anwa/esphome-r4875g1-3phase-charger/packages/display/pages/cooling.yaml

# ==============================================================================
# SHARED V6 LVGL PAGE: COOLING
# ==============================================================================
#
# Cooling overview for the three internal Huawei rectifier fans and the shared
# rear-compartment temperature, humidity and sea-level pressure measurements.
#
# Fan-mode controls express user intent through the shared UI command boundary.
# Controller-only external chassis-fan control is not exposed on this page.
#
# Runtime updates are handled by display/cooling.yaml.
# ==============================================================================

id: page_cooling
styles: style_page

widgets:

  # ---------------------------------------------------------------------------
  # COMPARTMENT ENVIRONMENT
  # ---------------------------------------------------------------------------

  - obj:
      x: 10
      y: 70
      width: 780
      height: 55
      styles: style_card

      widgets:
        - label:
            x: 10
            y: 10
            styles: style_title_label
            text: "COMPARTMENT"

        - label:
            id: ui_cooling_compartment_temperature
            x: 170
            y: 13
            width: 170
            text_align: CENTER
            text: "--.- °C"
            text_font: montserrat_24
            text_color: 0xFFFFFF

        - label:
            id: ui_cooling_compartment_humidity
            x: 375
            y: 13
            width: 170
            text_align: CENTER
            text: "--.- %"
            text_font: montserrat_24
            text_color: 0xFFFFFF

        - label:
            id: ui_cooling_compartment_pressure
            x: 580
            y: 13
            width: 180
            text_align: CENTER
            text: "----.- hPa"
            text_font: montserrat_24
            text_color: 0xFFFFFF

  # ---------------------------------------------------------------------------
  # RECTIFIER 1 FAN
  # ---------------------------------------------------------------------------

  - obj:
      x: 10
      y: 135
      width: 253
      height: 265
      styles: style_card

      widgets:
        - label:
            x: 10
            y: 10
            styles: style_title_label
            text: "RECTIFIER 1 FAN"

        - label:
            id: ui_cooling_r1_state
            x: 10
            y: 38
            width: 230
            text: "OFFLINE"
            text_font: montserrat_14
            text_color: 0x8B96A0

        - label:
            id: ui_cooling_r1_rpm
            x: 10
            y: 68
            width: 230
            text_align: CENTER
            text: "---- RPM"
            text_font: montserrat_24
            text_color: 0xFFFFFF

        - label:
            x: 10
            y: 108
            styles: style_desc_label
            text: "Minimum"

        - label:
            id: ui_cooling_r1_min_duty
            x: 130
            y: 106
            width: 110
            styles: style_value_label
            text: "--.- %"

        - label:
            x: 10
            y: 136
            styles: style_desc_label
            text: "Target"

        - label:
            id: ui_cooling_r1_target_duty
            x: 130
            y: 134
            width: 110
            styles: style_value_label
            text: "--.- %"

        - label:
            id: ui_cooling_r1_temperature
            x: 10
            y: 164
            width: 110
            text: "--.- °C"
            text_font: montserrat_16
            text_color: 0xDDE3E8

        - label:
            id: ui_cooling_r1_thermal
            x: 130
            y: 164
            width: 110
            text_align: RIGHT
            text: "--"
            text_font: montserrat_16
            text_color: 0x8B96A0

        - button:
            id: ui_cooling_r1_auto_button
            x: 10
            y: 205
            width: 110
            styles: style_dialog_button
            state:
              disabled: true

            widgets:
              - label:
                  align: CENTER
                  text: "AUTO"
                  text_font: montserrat_16

            on_short_click:
              - script.execute:
                  id: ui_command_rectifier_fan_auto
                  unit: 1

        - button:
            id: ui_cooling_r1_full_button
            x: 130
            y: 205
            width: 110
            styles: style_dialog_button
            state:
              disabled: true

            widgets:
              - label:
                  align: CENTER
                  text: "FULL"
                  text_font: montserrat_16

            on_short_click:
              - script.execute:
                  id: ui_command_rectifier_fan_full
                  unit: 1

  # ---------------------------------------------------------------------------
  # RECTIFIER 2 FAN
  # ---------------------------------------------------------------------------

  - obj:
      x: 273
      y: 135
      width: 253
      height: 265
      styles: style_card

      widgets:
        - label:
            x: 10
            y: 10
            styles: style_title_label
            text: "RECTIFIER 2 FAN"

        - label:
            id: ui_cooling_r2_state
            x: 10
            y: 38
            width: 230
            text: "OFFLINE"
            text_font: montserrat_14
            text_color: 0x8B96A0

        - label:
            id: ui_cooling_r2_rpm
            x: 10
            y: 68
            width: 230
            text_align: CENTER
            text: "---- RPM"
            text_font: montserrat_24
            text_color: 0xFFFFFF

        - label:
            x: 10
            y: 108
            styles: style_desc_label
            text: "Minimum"

        - label:
            id: ui_cooling_r2_min_duty
            x: 130
            y: 106
            width: 110
            styles: style_value_label
            text: "--.- %"

        - label:
            x: 10
            y: 136
            styles: style_desc_label
            text: "Target"

        - label:
            id: ui_cooling_r2_target_duty
            x: 130
            y: 134
            width: 110
            styles: style_value_label
            text: "--.- %"

        - label:
            id: ui_cooling_r2_temperature
            x: 10
            y: 164
            width: 110
            text: "--.- °C"
            text_font: montserrat_16
            text_color: 0xDDE3E8

        - label:
            id: ui_cooling_r2_thermal
            x: 130
            y: 164
            width: 110
            text_align: RIGHT
            text: "--"
            text_font: montserrat_16
            text_color: 0x8B96A0

        - button:
            id: ui_cooling_r2_auto_button
            x: 10
            y: 205
            width: 110
            styles: style_dialog_button
            state:
              disabled: true

            widgets:
              - label:
                  align: CENTER
                  text: "AUTO"
                  text_font: montserrat_16

            on_short_click:
              - script.execute:
                  id: ui_command_rectifier_fan_auto
                  unit: 2

        - button:
            id: ui_cooling_r2_full_button
            x: 130
            y: 205
            width: 110
            styles: style_dialog_button
            state:
              disabled: true

            widgets:
              - label:
                  align: CENTER
                  text: "FULL"
                  text_font: montserrat_16

            on_short_click:
              - script.execute:
                  id: ui_command_rectifier_fan_full
                  unit: 2

  # ---------------------------------------------------------------------------
  # RECTIFIER 3 FAN
  # ---------------------------------------------------------------------------

  - obj:
      x: 536
      y: 135
      width: 253
      height: 265
      styles: style_card

      widgets:
        - label:
            x: 10
            y: 10
            styles: style_title_label
            text: "RECTIFIER 3 FAN"

        - label:
            id: ui_cooling_r3_state
            x: 10
            y: 38
            width: 230
            text: "OFFLINE"
            text_font: montserrat_14
            text_color: 0x8B96A0

        - label:
            id: ui_cooling_r3_rpm
            x: 10
            y: 68
            width: 230
            text_align: CENTER
            text: "---- RPM"
            text_font: montserrat_24
            text_color: 0xFFFFFF

        - label:
            x: 10
            y: 108
            styles: style_desc_label
            text: "Minimum"

        - label:
            id: ui_cooling_r3_min_duty
            x: 130
            y: 106
            width: 110
            styles: style_value_label
            text: "--.- %"

        - label:
            x: 10
            y: 136
            styles: style_desc_label
            text: "Target"

        - label:
            id: ui_cooling_r3_target_duty
            x: 130
            y: 134
            width: 110
            styles: style_value_label
            text: "--.- %"

        - label:
            id: ui_cooling_r3_temperature
            x: 10
            y: 164
            width: 110
            text: "--.- °C"
            text_font: montserrat_16
            text_color: 0xDDE3E8

        - label:
            id: ui_cooling_r3_thermal
            x: 130
            y: 164
            width: 110
            text_align: RIGHT
            text: "--"
            text_font: montserrat_16
            text_color: 0x8B96A0

        - button:
            id: ui_cooling_r3_auto_button
            x: 10
            y: 205
            width: 110
            styles: style_dialog_button
            state:
              disabled: true

            widgets:
              - label:
                  align: CENTER
                  text: "AUTO"
                  text_font: montserrat_16

            on_short_click:
              - script.execute:
                  id: ui_command_rectifier_fan_auto
                  unit: 3

        - button:
            id: ui_cooling_r3_full_button
            x: 130
            y: 205
            width: 110
            styles: style_dialog_button
            state:
              disabled: true

            widgets:
              - label:
                  align: CENTER
                  text: "FULL"
                  text_font: montserrat_16

            on_short_click:
              - script.execute:
                  id: ui_command_rectifier_fan_full
                  unit: 3
