anwa/esphome-r4875g1-3phase-charger/r4875g1-3phase-charger.yaml

# ==============================================================================
# R4875G1 THREE-PHASE CHARGER - V6 CONTROLLER HARDWARE
# ==============================================================================
#
# Target controller:
#   Waveshare ESP32-S3-Touch-LCD-7
#   ESP32-S3 N16R8
#
# Memory:
#   Flash -> 16 MB
#   PSRAM -> 8 MB Octal
#
# Integrated board hardware:
#   - 7-inch 800x480 RGB IPS display
#   - GT911 capacitive touch controller
#   - CH422G I/O expander
#   - onboard CAN transceiver
#   - onboard RS485 interface
#   - TF card interface
#   - native USB and USB-to-UART
#
# External hardware:
#   - dedicated external I2C bus on GPIO44 / GPIO43
#   - MCP23017 I/O expander @ 0x20
#   - BME280 compartment environment sensor @ 0x76
#   - EMC2101 external cooling-fan controller @ 0x4C
#   - backup rotary encoder on GPIO11 / GPIO12 / GPIO13
#   - external three/four-pin cooling-fan interface
#   - 1S lithium controller backup battery on J3
#   - battery-voltage measurement through TP1 / J8 AD / GPIO6
#
# The V6 Charger Controller retains the proven three-rectifier CAN control architecture
# while using the Waveshare display controller as the local standalone UI.
# ==============================================================================

# ==============================================================================
# THREE-PHASE R4875G1 CHARGER CONTROLLER - ARCHITECTURE OVERVIEW
# ==============================================================================
#
# This ESPHome firmware controls three Huawei R4875G1 rectifier units used as
# a three-phase battery charger. Each rectifier is supplied from one AC phase;
# their DC outputs are connected in parallel to the same battery bus.
#
# Data path:
#
#   R4875G1 Unit 1 / 2 / 3
#          |
#          | extended 29-bit CAN frames @ 125 kbit/s
#          v
#   ESP32-S3 CAN decoder
#          |
#          +--> individual unit telemetry sensors
#          |      AC/DC power, voltage, current, frequency, temperatures, state
#          |
#          +--> per-unit CAN watchdogs (can_com_ok_1..3)
#          |
#          +--> CAN-aware charger-wide aggregate telemetry
#          |
#          +--> TFT display / Home Assistant / MQTT
#
# Local control path:
#
#   GT911 touchscreen / LVGL interface
#          |
#          +--> charger-wide voltage and power setpoints
#          +--> charger and per-unit START/STOP controls
#          +--> fallback voltage/current adjustment
#
# The backup rotary encoder provides a local staged editor for the charger-wide
# DC voltage and nominal DC sum-power setpoints. Saved values use the same
# authoritative command path as the touchscreen. A deliberate long button
# press provides local charger START/STOP while the setpoint editor is idle.
# Power requests use the existing authoritative Charger Controller command
# paths rather than implementing separate CAN or safety logic.
#
# Offline operation:
#
# Wi-Fi, MQTT and Home Assistant are optional for core charger operation.
# Network reboot timeouts are disabled so a dead or isolated site network cannot
# prevent the ESP32 from controlling the charger during a blackstart.
#
# CAN value scaling:
#
# Most voltage/telemetry values use a fixed-point scale of 1024:
#     engineering_value = raw_CAN_value / 1024
#     raw_CAN_value     = engineering_value * 1024
#
# DC current commands use current_scaling_factor.
#
# Until all currently reachable rectifiers have fresh capability data, the
# controller uses the conservative 75 A protocol scale:
#
#     current_scaling_factor = 1024 / 75
#
# Once capability discovery is complete, command scaling is derived from the
# reachable rectifier capabilities.
#
# effective_dc_current_limit is maintained independently and enforces the
# lowest supported current capability across the currently reachable units.
# This keeps mixed-capability installations within the limit of the weakest
# available rectifier.
#
# Communication health:
#
# Valid per-unit CAN activity refreshes last_can_rx_1..3. During normal
# operation cyclic telemetry provides the heartbeat; valid property frames also
# refresh it while discovery temporarily suspends cyclic polling.
#
# If no valid CAN activity is received within can_watchdog_timeout_ms,
# can_com_ok_x becomes false. Display and aggregate logic then ignore stale
# values from that unit.
# ==============================================================================

substitutions:
  # ---------------------------------------------------------------------------
  # PROJECT IDENTITY
  # ---------------------------------------------------------------------------

  mqtt_command_prefix: "HG/DG/Technik/Charger"
  fallback_ap_ssid: "Charger Fallback Hotspot"
  diagnostics_device_label: "Controller"

  # ---------------------------------------------------------------------------
  # INSTALLATION ENVIRONMENT
  # ---------------------------------------------------------------------------
  # Fixed site altitude used for standard-atmosphere sea-level pressure
  # correction of the compartment BME280 station-pressure measurement.
  installation_altitude_m: "316.0"

  # ---------------------------------------------------------------------------
  # V6 CHARGER CONTROLLER GPIO MAP
  # ---------------------------------------------------------------------------

  pin_touch_irq: "GPIO4"
  pin_i2c_sda: "GPIO8"
  pin_i2c_scl: "GPIO9"
  pin_external_i2c_sda: "GPIO44"
  pin_external_i2c_scl: "GPIO43"
  pin_can_tx: "GPIO20"
  pin_can_rx: "GPIO19"
  pin_battery_adc: "GPIO6"

  # GPIO11/GPIO12/GPIO13 are the unused TF-card SPI pins.
  pin_backup_encoder_a: "GPIO11"
  pin_backup_encoder_b: "GPIO12"
  pin_backup_encoder_button: "GPIO13"

  # MCP23017 pin allocation.
  mcp_fan_enable_pin: "0"
  mcp_fan1_tach_pin: "1"
  mcp_fan2_tach_pin: "2"

  # ---------------------------------------------------------------------------
  # BACKUP ROTARY ENCODER
  # ---------------------------------------------------------------------------

  # One output step per complete quadrature cycle.
  backup_encoder_resolution: "1"

  # Pending setpoint edits are discarded after 15 seconds without activity.
  backup_encoder_edit_timeout_ms: "15000"

  # Transient encoder status overlays remain visible for 1.5 seconds.
  backup_encoder_ui_status_timeout_ms: "1500"

  # ---------------------------------------------------------------------------
  # DISPLAY DEFAULTS
  # ---------------------------------------------------------------------------

  ui_local_battery_label: "CTRL"
  display_idle_timeout: "60s"
  display_motion_entity: "binary_sensor.hg_og_buro_hg_og_buro_precense_occupancy"

  # ---------------------------------------------------------------------------
  # EXTERNAL COOLING-FAN DEFAULTS
  # ---------------------------------------------------------------------------

  # EMC2101 PWM configuration:
  #   360 kHz / (2 × 7 × 1) ≈ 25.7 kHz
  cooling_fan_pwm_resolution: "7"
  cooling_fan_pwm_divider: "1"

  cooling_fan_default_pwm_percent: "100.0"

  # Used for the two MCP23017-based tachometer inputs.
  cooling_fan_tach_pulses_per_revolution: "2.0"

  # ---------------------------------------------------------------------------
  # DC OPERATING LIMITS
  # ---------------------------------------------------------------------------

  # Absolute supported per-rectifier project ceiling.
  project_max_dc_current_a: "75.0"

  # Conservative ceiling until every currently reachable rectifier has a
  # freshly confirmed maximum-current capability.
  failsafe_dc_current_a: "50.0"

  minimum_dc_current_a: "1.0"

  dc_voltage_default_v: "53.0"

  # ---------------------------------------------------------------------------
  # THERMAL DERATING
  # ---------------------------------------------------------------------------

  thermal_warn1_c: "70.0"
  thermal_warn1_reset_c: "65.0"
  thermal_warn1_limit_a: "50.0"

  thermal_warn2_c: "80.0"
  thermal_warn2_reset_c: "75.0"
  thermal_warn2_limit_a: "30.0"

  overtemp_trip_c: "90.0"
  overtemp_reset_c: "80.0"

  # ---------------------------------------------------------------------------
  # THERMAL STATE CODES
  # ---------------------------------------------------------------------------

  thermal_state_normal: "0"
  thermal_state_warn1: "1"
  thermal_state_warn2: "2"
  thermal_state_lockout: "3"

  # Ignore near-idle input power where calculated efficiency becomes unstable.
  efficiency_min_ac_power_w: "100.0"

  # ---------------------------------------------------------------------------
  # PROTOCOL SCALING
  # ---------------------------------------------------------------------------

  protocol_value_scale: "1024"
  fan_duty_counts_per_percent: "256.0"

  # ---------------------------------------------------------------------------
  # RECTIFIER CONTROL-STATE CODES
  # ---------------------------------------------------------------------------
  # Internal lifecycle state used independently for each rectifier.
  #
  # OFFLINE:
  #   No usable communication / unit not operationally released.
  #
  # DISCOVERING:
  #   CAN communication has been detected, but discovery and validation have
  #   not yet completed.
  #
  # ONLINE:
  #   Discovery completed successfully and the unit is ready for normal
  #   operational handling.
  # ---------------------------------------------------------------------------

  rectifier_state_offline: "0"
  rectifier_state_discovering: "1"
  rectifier_state_online: "2"

  # ---------------------------------------------------------------------------
  # CAN COMMUNICATION
  # ---------------------------------------------------------------------------

  # RX queue depth must accommodate the largest observed multi-frame property
  # response without dropping frames.
  can_rx_queue_len: "64"

  # Normal runtime CAN watchdog.
  can_watchdog_timeout_ms: "3000"

  # Grace period after property discovery so normal cyclic polling has enough
  # time to resume before lifecycle connectivity is evaluated again.
  property_poll_resume_grace_ms: "2000"

  live_telemetry_timeout: "5s"

  telemetry_poll_interval: "577ms"
  fan_query_delay: "27ms"
  unit_2_poll_gap: "156ms"
  unit_3_poll_gap: "166ms"

  # Offline rectifiers are probed round-robin. One unit is considered every
  # five seconds, resulting in a maximum probe interval of approximately
  # 15 seconds per offline rectifier.
  offline_probe_slot_interval: "5s"

  can_recovery_check_interval: "2s"
  setpoint_refresh_interval: "30s"

  # ---------------------------------------------------------------------------
  # SLOW-CHANGING TELEMETRY
  # ---------------------------------------------------------------------------
  #
  # Stable diagnostic values are forwarded immediately when they change and
  # repeated periodically so time-series consumers retain a recent sample even
  # when the underlying charger state remains unchanged.
  # ---------------------------------------------------------------------------

  telemetry_heartbeat_interval: "60min"

  # ---------------------------------------------------------------------------
  # DISCOVERY RETRY POLICY
  # ---------------------------------------------------------------------------

  property_discovery_attempts: "3"
  capability_discovery_attempts: "10"
  discovery_retry_delay: "1s"
  discovery_startup_delay: "5s"
  property_bus_quiet_delay: "500ms"

# ==============================================================================
# FIRMWARE PACKAGE ASSEMBLY
# ==============================================================================
#
# Composes shared board hardware, Charger Controller hardware and the charger
# runtime packages, then instantiates one rectifier package per charger unit.
# ==============================================================================

packages:
  version: !include packages/version.yaml
  shared_ui_contract: !include packages/shared/ui-contract.yaml

  shared_core: !include packages/shared/core.yaml
  shared_local_diagnostics: !include packages/shared/local-diagnostics.yaml
  shared_hardware: !include packages/shared/hardware.yaml
  shared_ui_model: !include packages/shared/ui-model.yaml
  shared_ui_rectifier_1: !include
    file: packages/shared/ui-rectifier-unit.yaml
    vars:
      ui_unit: "1"

  shared_ui_rectifier_2: !include
    file: packages/shared/ui-rectifier-unit.yaml
    vars:
      ui_unit: "2"

  shared_ui_rectifier_3: !include
    file: packages/shared/ui-rectifier-unit.yaml
    vars:
      ui_unit: "3"

  shared_battery_monitoring: !include packages/shared/battery-monitoring.yaml

  controller_hardware: !include packages/controller/hardware.yaml
  controller_environment: !include packages/controller/environment.yaml
  controller_ha_contract: !include packages/controller/ha-contract.yaml
  controller_mqtt: !include packages/controller/mqtt.yaml
  controller_ui_backend: !include packages/controller/ui-backend.yaml
  controller_ui_rectifier_1: !include
    file: packages/controller/ui-rectifier-backend.yaml
    vars:
      ui_unit: "1"

  controller_ui_rectifier_2: !include
    file: packages/controller/ui-rectifier-backend.yaml
    vars:
      ui_unit: "2"

  controller_ui_rectifier_3: !include
    file: packages/controller/ui-rectifier-backend.yaml
    vars:
      ui_unit: "3"
  controller_ui_commands: !include packages/controller/ui-commands.yaml

  controller_encoder: !include packages/controller/encoder.yaml

  cooling: !include packages/cooling.yaml
  display: !include packages/display.yaml
  controller_encoder_ui: !include packages/controller/encoder-ui.yaml

  # Optional target-specific Home Assistant motion source for display activity.
  # Remove this package entry to use only the original touch/idle behavior.
  display_motion: !include
    file: packages/display/homeassistant-motion.yaml
    vars:
      display_motion_entity: ${display_motion_entity}

  controls: !include packages/controls.yaml
  rectifier_shared: !include packages/rectifier-shared.yaml

  rectifier_unit_1: !include
    file: packages/rectifier-unit.yaml
    vars:
      ru_unit: "1"

  rectifier_unit_2: !include
    file: packages/rectifier-unit.yaml
    vars:
      ru_unit: "2"

  rectifier_unit_3: !include
    file: packages/rectifier-unit.yaml
    vars:
      ru_unit: "3"

# ==============================================================================
# ESPHOME DEVICE IDENTITY AND BOOT ACTIONS
# ==============================================================================
#
# Defines the device identity used by ESPHome/Home Assistant.
# The boot hook initializes rectifier lifecycle and shared diagnostic states.
# ==============================================================================

esphome:
  name: hg-dg-technik-charger
  friendly_name: HG|DG|Technik|Charger
  min_version: 2026.8.2

  project:
    name: "anwa.r4875-charger"
    version: "${firmware_version}"

  on_boot:
    then:
      # Until valid rectifier status frames have been received, the actual
      # power state of each unit is unknown.
      - lambda: |-
          id(power_state_1).publish_state("UNKNOWN");
          id(power_state_2).publish_state("UNKNOWN");
          id(power_state_3).publish_state("UNKNOWN");

          id(thermal_state_text_1).publish_state("NORMAL");
          id(thermal_state_text_2).publish_state("NORMAL");
          id(thermal_state_text_3).publish_state("NORMAL");

          // Publish the conservative 50 A failsafe ceiling until the
          // capabilities of all currently reachable rectifiers are known.
          id(effective_dc_current_limit_sensor).publish_state(
            id(effective_dc_current_limit)
          );

      # Every rectifier starts in OFFLINE control state after an ESP reboot.
      # A unit must be detected and successfully discovered before it can later
      # transition to ONLINE.
      - script.execute:
          id: set_rectifier_control_state
          unit: 1
          state: ${rectifier_state_offline}

      - script.execute:
          id: set_rectifier_control_state
          unit: 2
          state: ${rectifier_state_offline}

      - script.execute:
          id: set_rectifier_control_state
          unit: 3
          state: ${rectifier_state_offline}

# ==============================================================================
# PROJECT-WIDE / AGGREGATE SENSORS
# ==============================================================================
#
# Charger-wide aggregate telemetry that does not belong to one parameterized
# rectifier instance. Charger-side environment sensing is owned by
# controller/environment.yaml.
# ==============================================================================

sensor:

  # ---------------------------------------------------------------------------
  # REQUESTED DC CURRENT LIMIT
  # ---------------------------------------------------------------------------
  #
  # Read-only telemetry mirror of the charger-wide DC current control. The
  # number entity remains the authoritative control while this sensor provides
  # change-driven and periodic history data for time-series consumers.
  # ---------------------------------------------------------------------------

  - platform: template
    name: "Requested DC Current Limit"
    id: requested_dc_current_limit_sensor
    unit_of_measurement: "A"
    device_class: current
    entity_category: diagnostic
    state_class: measurement
    accuracy_decimals: 1
    update_interval: 1s
    lambda: |-
      return id(set_dc_current_limit).state;
    filters:
      - or:
          - delta: 0.0
          - heartbeat: ${telemetry_heartbeat_interval}
    icon: "mdi:current-dc"

  # ---------------------------------------------------------------------------
  # EFFECTIVE DC CURRENT LIMIT
  # ---------------------------------------------------------------------------
  #
  # Runtime hardware/capability ceiling shared by all active-current paths.
  # ---------------------------------------------------------------------------

  - platform: template
    name: "Effective DC Current Limit"
    id: effective_dc_current_limit_sensor
    unit_of_measurement: "A"
    device_class: current
    entity_category: diagnostic
    accuracy_decimals: 1
    update_interval: never
    filters:
      - or:
          - delta: 0.0
          - heartbeat: ${telemetry_heartbeat_interval}
    icon: "mdi:current-dc"

  # ---------------------------------------------------------------------------
  # THERMAL / APPLIED CURRENT DIAGNOSTICS
  # ---------------------------------------------------------------------------

  - platform: template
    name: "Thermal DC Current Limit"
    id: thermal_dc_current_limit_sensor
    unit_of_measurement: "A"
    device_class: current
    entity_category: diagnostic
    accuracy_decimals: 1
    update_interval: 1s
    lambda: 'return id(thermal_dc_current_limit);'
    filters:
      - or:
          - delta: 0.0
          - heartbeat: ${telemetry_heartbeat_interval}
    icon: "mdi:thermometer-alert"

  - platform: template
    name: "Applied DC Current Limit"
    id: applied_dc_current_limit_sensor
    unit_of_measurement: "A"
    device_class: current
    state_class: measurement
    accuracy_decimals: 1
    update_interval: 1s
    lambda: |-
      const float requested = id(set_dc_current_limit).state;
      if (isnan(requested)) return NAN;
      float applied = std::min(requested, id(effective_dc_current_limit));
      applied = std::min(applied, id(thermal_dc_current_limit));
      return applied;
    filters:
      - or:
          - delta: 0.0
          - heartbeat: ${telemetry_heartbeat_interval}
    icon: "mdi:current-dc"

  # ---------------------------------------------------------------------------
  # COMBINED AC POWER ALL UNITS
  # ---------------------------------------------------------------------------
  #
  # CAN-aware AC-input power total from reachable units with valid telemetry.
  # ---------------------------------------------------------------------------

  - platform: template
    name: "Combined AC Power All Units"
    id: combined_ac_power
    unit_of_measurement: "kW"
    device_class: power
    state_class: measurement
    accuracy_decimals: 3
    update_interval: 1s
    filters:
      - multiply: 0.001
    lambda: |-
      float power = 0.0f;
      int valid_units = 0;

      if (id(can_com_ok_1).state &&
          !isnan(id(ac_power_1).state)) {
        power += id(ac_power_1).state;
        valid_units++;
      }

      if (id(can_com_ok_2).state &&
          !isnan(id(ac_power_2).state)) {
        power += id(ac_power_2).state;
        valid_units++;
      }

      if (id(can_com_ok_3).state &&
          !isnan(id(ac_power_3).state)) {
        power += id(ac_power_3).state;
        valid_units++;
      }

      if (valid_units == 0) {
        return NAN;
      }

      return power;
    icon: "mdi:flash"

  # ---------------------------------------------------------------------------
  # AVERAGE AC VOLTAGE ALL UNITS
  # ---------------------------------------------------------------------------
  #
  # Average AC input voltage across all reachable rectifiers with valid
  # telemetry. Each rectifier is connected to a separate AC phase.
  # ---------------------------------------------------------------------------

  - platform: template
    name: "Average AC Voltage All Units"
    id: average_ac_voltage
    unit_of_measurement: "V"
    device_class: voltage
    state_class: measurement
    accuracy_decimals: 3
    update_interval: 1s
    lambda: |-
      float voltage = 0.0f;
      int valid_units = 0;

      if (id(can_com_ok_1).state &&
          !isnan(id(ac_voltage_1).state)) {
        voltage += id(ac_voltage_1).state;
        valid_units++;
      }

      if (id(can_com_ok_2).state &&
          !isnan(id(ac_voltage_2).state)) {
        voltage += id(ac_voltage_2).state;
        valid_units++;
      }

      if (id(can_com_ok_3).state &&
          !isnan(id(ac_voltage_3).state)) {
        voltage += id(ac_voltage_3).state;
        valid_units++;
      }

      if (valid_units == 0) {
        return NAN;
      }

      return voltage / valid_units;
    icon: "mdi:sine-wave"

  # ---------------------------------------------------------------------------
  # AVERAGE AC CURRENT ALL UNITS
  # ---------------------------------------------------------------------------
  #
  # Average AC phase current across all reachable rectifiers with valid
  # telemetry. Currents from the three independent phases are not summed.
  # ---------------------------------------------------------------------------

  - platform: template
    name: "Average AC Current All Units"
    id: average_ac_current
    unit_of_measurement: "A"
    device_class: current
    state_class: measurement
    accuracy_decimals: 3
    update_interval: 1s
    lambda: |-
      float current = 0.0f;
      int valid_units = 0;

      if (id(can_com_ok_1).state &&
          !isnan(id(ac_current_1).state)) {
        current += id(ac_current_1).state;
        valid_units++;
      }

      if (id(can_com_ok_2).state &&
          !isnan(id(ac_current_2).state)) {
        current += id(ac_current_2).state;
        valid_units++;
      }

      if (id(can_com_ok_3).state &&
          !isnan(id(ac_current_3).state)) {
        current += id(ac_current_3).state;
        valid_units++;
      }

      if (valid_units == 0) {
        return NAN;
      }

      return current / valid_units;
    icon: "mdi:current-ac"

  # ---------------------------------------------------------------------------
  # COMBINED DC POWER ALL UNITS
  # ---------------------------------------------------------------------------
  #
  # CAN-aware DC power total with the same stale-data protection as the AC
  # total. The lambda sums watts and the multiply filter converts W to kW.
  # ---------------------------------------------------------------------------

  - platform: template
    name: "Combined DC Power All Units"
    id: combined_dc_power
    unit_of_measurement: "kW"
    device_class: power
    state_class: measurement
    accuracy_decimals: 3
    update_interval: 1s
    filters:
      - multiply: 0.001
    lambda: |-
      float power = 0.0f;
      int valid_units = 0;

      if (id(can_com_ok_1).state &&
          !isnan(id(dc_power_1).state)) {
        power += id(dc_power_1).state;
        valid_units++;
      }

      if (id(can_com_ok_2).state &&
          !isnan(id(dc_power_2).state)) {
        power += id(dc_power_2).state;
        valid_units++;
      }

      if (id(can_com_ok_3).state &&
          !isnan(id(dc_power_3).state)) {
        power += id(dc_power_3).state;
        valid_units++;
      }

      // No valid CAN data available
      if (valid_units == 0) {
        return NAN;
      }

      return power;
    icon: "mdi:flash"

  # ---------------------------------------------------------------------------
  # AVAILABLE UNITS
  # ---------------------------------------------------------------------------
  #
  # Number of rectifier units currently providing valid CAN communication.
  # ---------------------------------------------------------------------------

  - platform: template
    name: "Available Units"
    id: available_units
    state_class: measurement
    accuracy_decimals: 0
    update_interval: 1s
    filters:
      - or:
          - delta: 0.0
          - heartbeat: ${telemetry_heartbeat_interval}
    lambda: |-
      int count = 0;

      if (id(can_com_ok_1).state) {
        count++;
      }

      if (id(can_com_ok_2).state) {
        count++;
      }

      if (id(can_com_ok_3).state) {
        count++;
      }

      return count;
    icon: "mdi:server-network"

  # ---------------------------------------------------------------------------
  # RUNNING UNITS
  # ---------------------------------------------------------------------------
  #
  # Number of reachable rectifiers currently reporting their power state as ON.
  # A unit with stale CAN communication or an unknown power state is not counted
  # as running.
  # ---------------------------------------------------------------------------

  - platform: template
    name: "Running Units"
    id: running_units
    state_class: measurement
    accuracy_decimals: 0
    update_interval: 500ms
    filters:
      - or:
          - delta: 0.0
          - heartbeat: ${telemetry_heartbeat_interval}
    lambda: |-
      int count = 0;

      if (id(can_com_ok_1).state &&
          id(power_state_1).state == "ON") {
        count++;
      }

      if (id(can_com_ok_2).state &&
          id(power_state_2).state == "ON") {
        count++;
      }

      if (id(can_com_ok_3).state &&
          id(power_state_3).state == "ON") {
        count++;
      }

      return count;
    icon: "mdi:power"

  # ---------------------------------------------------------------------------
  # COMBINED DC CURRENT ALL UNITS
  # ---------------------------------------------------------------------------
  #
  # Sum of DC output current from all reachable rectifiers with valid telemetry.
  # ---------------------------------------------------------------------------

  - platform: template
    name: "Combined DC Current All Units"
    id: combined_dc_current
    unit_of_measurement: "A"
    device_class: current
    state_class: measurement
    accuracy_decimals: 2
    update_interval: 1s
    lambda: |-
      float current = 0.0f;
      int valid_units = 0;

      if (id(can_com_ok_1).state &&
          !isnan(id(dc_current_1).state)) {
        current += id(dc_current_1).state;
        valid_units++;
      }

      if (id(can_com_ok_2).state &&
          !isnan(id(dc_current_2).state)) {
        current += id(dc_current_2).state;
        valid_units++;
      }

      if (id(can_com_ok_3).state &&
          !isnan(id(dc_current_3).state)) {
        current += id(dc_current_3).state;
        valid_units++;
      }

      if (valid_units == 0) {
        return NAN;
      }

      return current;
    icon: "mdi:current-dc"

  # ---------------------------------------------------------------------------
  # AVERAGE DC VOLTAGE ALL UNITS
  # ---------------------------------------------------------------------------
  #
  # Average DC output voltage across all reachable rectifiers.
  #
  # The rectifier outputs are connected in parallel, so their voltages should
  # normally be nearly identical.
  # ---------------------------------------------------------------------------

  - platform: template
    name: "Average DC Voltage All Units"
    id: average_dc_voltage
    unit_of_measurement: "V"
    device_class: voltage
    state_class: measurement
    accuracy_decimals: 2
    update_interval: 1s
    lambda: |-
      float voltage = 0.0f;
      int valid_units = 0;

      if (id(can_com_ok_1).state &&
          !isnan(id(dc_voltage_1).state)) {
        voltage += id(dc_voltage_1).state;
        valid_units++;
      }

      if (id(can_com_ok_2).state &&
          !isnan(id(dc_voltage_2).state)) {
        voltage += id(dc_voltage_2).state;
        valid_units++;
      }

      if (id(can_com_ok_3).state &&
          !isnan(id(dc_voltage_3).state)) {
        voltage += id(dc_voltage_3).state;
        valid_units++;
      }

      if (valid_units == 0) {
        return NAN;
      }

      return voltage / valid_units;
    icon: "mdi:current-dc"

  # ---------------------------------------------------------------------------
  # HIGHEST OUTPUT TEMPERATURE ALL UNITS
  # ---------------------------------------------------------------------------
  #
  # Reports the hottest currently reachable rectifier.
  # ---------------------------------------------------------------------------

  - platform: template
    name: "Highest Output Temperature All Units"
    id: highest_output_temperature
    unit_of_measurement: "°C"
    device_class: temperature
    state_class: measurement
    accuracy_decimals: 1
    update_interval: 1s
    lambda: |-
      float highest = 0.0f;
      bool valid = false;

      if (id(can_com_ok_1).state &&
          !isnan(id(output_temperature_1).state)) {
        highest = id(output_temperature_1).state;
        valid = true;
      }

      if (id(can_com_ok_2).state &&
          !isnan(id(output_temperature_2).state)) {
        if (!valid ||
            id(output_temperature_2).state > highest) {
          highest = id(output_temperature_2).state;
        }
        valid = true;
      }

      if (id(can_com_ok_3).state &&
          !isnan(id(output_temperature_3).state)) {
        if (!valid ||
            id(output_temperature_3).state > highest) {
          highest = id(output_temperature_3).state;
        }
        valid = true;
      }

      if (!valid) {
        return NAN;
      }

      return highest;
    icon: "mdi:thermometer-high"

  # ---------------------------------------------------------------------------
  # CONVERSION EFFICIENCY ALL UNITS
  # ---------------------------------------------------------------------------
  #
  # Calculates DC output power divided by AC input power.
  #
  # Only units that simultaneously provide valid AC and DC power telemetry are
  # included. Values below 100 W AC input are ignored because efficiency
  # becomes meaningless and unstable close to idle operation.
  # ---------------------------------------------------------------------------

  - platform: template
    name: "Conversion Efficiency All Units"
    id: conversion_efficiency
    unit_of_measurement: "%"
    state_class: measurement
    accuracy_decimals: 1
    update_interval: 1s
    lambda: |-
      float ac_power = 0.0f;
      float dc_power = 0.0f;
      int valid_units = 0;

      if (id(can_com_ok_1).state &&
          !isnan(id(ac_power_1).state) &&
          !isnan(id(dc_power_1).state)) {
        ac_power += id(ac_power_1).state;
        dc_power += id(dc_power_1).state;
        valid_units++;
      }

      if (id(can_com_ok_2).state &&
          !isnan(id(ac_power_2).state) &&
          !isnan(id(dc_power_2).state)) {
        ac_power += id(ac_power_2).state;
        dc_power += id(dc_power_2).state;
        valid_units++;
      }

      if (id(can_com_ok_3).state &&
          !isnan(id(ac_power_3).state) &&
          !isnan(id(dc_power_3).state)) {
        ac_power += id(ac_power_3).state;
        dc_power += id(dc_power_3).state;
        valid_units++;
      }

      if (valid_units == 0 ||
          ac_power < ${efficiency_min_ac_power_w}f) {
        return NAN;
      }

      return (dc_power / ac_power) * 100.0f;
    icon: "mdi:gauge"

  # ---------------------------------------------------------------------------
  # AC ENERGY TODAY
  # ---------------------------------------------------------------------------
  #
  # Daily AC input energy integrated from the CAN-aware combined AC power.
  # ---------------------------------------------------------------------------

  - platform: total_daily_energy
    name: "AC Energy Today"
    power_id: combined_ac_power
    time_id: sntp_time
    unit_of_measurement: "kWh"
    device_class: energy
    state_class: total_increasing
    accuracy_decimals: 3
    icon: "mdi:counter"

  # ---------------------------------------------------------------------------
  # DC ENERGY TODAY
  # ---------------------------------------------------------------------------
  #
  # Daily DC output energy integrated from the CAN-aware combined DC power.
  # ---------------------------------------------------------------------------

  - platform: total_daily_energy
    name: "DC Energy Today"
    power_id: combined_dc_power
    time_id: sntp_time
    unit_of_measurement: "kWh"
    device_class: energy
    state_class: total_increasing
    accuracy_decimals: 3
    icon: "mdi:counter"

# ==============================================================================
# PROJECT-WIDE BINARY SENSORS
# ==============================================================================
#
# Charger-wide diagnostic states that do not belong to one rectifier instance.
# ==============================================================================

binary_sensor:

  # ---------------------------------------------------------------------------
  # RECTIFIER CAPABILITY MISMATCH
  # ---------------------------------------------------------------------------
  #
  # Diagnostic problem indicator comparing the maximum-current capability
  # reported by all three rectifiers.
  #
  # State:
  #   unknown = not all three current capabilities have been confirmed
  #   OFF     = all three capabilities match
  #   ON      = at least one rectifier reports a different capability
  #
  # The state is published by evaluate_rectifier_capabilities whenever fresh
  # capability data is received.
  # ---------------------------------------------------------------------------

  - platform: template
    name: "Rectifier Capability Mismatch"
    id: rectifier_capability_mismatch
    device_class: problem
    entity_category: diagnostic
    icon: "mdi:alert-circle-outline"
