anwa/esphome-r4875g1-3phase-charger/packages/display/pages/rectifiers.yaml

# ==============================================================================
# LVGL PAGE: RECTIFIERS
# ==============================================================================
#
# Three-column overview of the individual Huawei rectifiers.
#
# Each card shows the current lifecycle, power state and primary AC/DC
# telemetry and provides START/STOP and detail-page access for that unit.
#
# Runtime updates are handled by display/rectifiers.yaml.
# ==============================================================================

id: page_rectifiers
styles: style_page

widgets:

  # ---------------------------------------------------------------------------
  # RECTIFIER 1
  # ---------------------------------------------------------------------------

  - obj:
      x: 10
      y: 70
      width: 253
      height: 330
      styles: style_card

      widgets:
        - label:
            x: 10
            y: 10
            styles: style_title_label
            text: "RECTIFIER 1"

        - label:
            id: ui_rectifier_1_lifecycle
            x: 10
            y: 43
            text: "OFFLINE"
            text_font: montserrat_16
            text_color: 0x8B96A0

        - label:
            id: ui_rectifier_1_power_state
            x: 165
            y: 43
            width: 65
            text_align: RIGHT
            text: "--"
            text_font: montserrat_16
            text_color: 0x8B96A0

        - label:
            x: 10
            y: 82
            styles: style_desc_label
            text: "AC"

        - label:
            id: ui_rectifier_1_ac_voltage
            x: 65
            y: 80
            text: "230 V"
            text_font: montserrat_18
            text_color: 0xDDE3E8

        - label:
            id: ui_rectifier_1_ac_current
            x: 150
            y: 80
            text: "5.2 A"
            text_font: montserrat_18
            text_color: 0xDDE3E8

        - label:
            x: 10
            y: 122
            styles: style_desc_label
            text: "DC"

        - label:
            id: ui_rectifier_1_dc_voltage
            x: 65
            y: 120
            text: "53.1 V"
            text_font: montserrat_18
            text_color: 0xDDE3E8

        - label:
            id: ui_rectifier_1_dc_current
            x: 150
            y: 120
            text: "22.4 A"
            text_font: montserrat_18
            text_color: 0xDDE3E8

        - label:
            id: ui_rectifier_1_dc_power
            x: 65
            y: 151
            text: "--.-- kW"
            text_font: montserrat_20
            text_color: 0xFFFFFF

        - label:
            x: 10
            y: 194
            styles: style_desc_label
            text: "OUT"

        - label:
            id: ui_rectifier_1_temperature
            x: 65
            y: 192
            text: "--.- °C"
            text_font: montserrat_18
            text_color: 0xDDE3E8

        - button:
            id: ui_rectifier_1_power_button
            x: 10
            y: 270
            width: 143
            styles: style_dialog_button

            widgets:
              - label:
                  id: ui_rectifier_1_power_button_label
                  align: CENTER
                  text: "UNAVAILABLE"
                  text_font: montserrat_16

            on_short_click:
              - if:
                  condition:
                    lambda: |-
                        return
                          id(ui_model_data_available).state &&
                          id(ui_model_rectifier_1_online).state &&
                          id(ui_model_rectifier_1_power_state).state == "ON";

                  then:
                    - lvgl.widget.show: ui_stop_rectifier_1_dialog

                  else:
                    - lvgl.widget.show: ui_start_rectifier_1_dialog

        - button:
            x: 163
            y: 270
            width: 80
            styles: style_dialog_button

            widgets:
              - label:
                  align: CENTER
                  text: "DETAIL"
                  text_font: montserrat_16

            on_short_click:
              - lambda: |-
                  id(rectifier_detail_unit) = 1;
                  id(ui_active_page) = 2;

              - lvgl.page.show: page_rectifier_detail

              - script.execute:
                  id: refresh_rectifier_detail

  # ---------------------------------------------------------------------------
  # RECTIFIER 2
  # ---------------------------------------------------------------------------

  - obj:
      x: 273
      y: 70
      width: 253
      height: 330
      styles: style_card

      widgets:
        - label:
            x: 10
            y: 10
            styles: style_title_label
            text: "RECTIFIER 2"

        - label:
            id: ui_rectifier_2_lifecycle
            x: 10
            y: 43
            text: "OFFLINE"
            text_font: montserrat_16
            text_color: 0x8B96A0

        - label:
            id: ui_rectifier_2_power_state
            x: 165
            y: 43
            width: 65
            text_align: RIGHT
            text: "--"
            text_font: montserrat_16
            text_color: 0x8B96A0

        - label:
            x: 10
            y: 82
            styles: style_desc_label
            text: "AC"

        - label:
            id: ui_rectifier_2_ac_voltage
            x: 65
            y: 80
            text: "--- V"
            text_font: montserrat_18
            text_color: 0x8B96A0

        - label:
            id: ui_rectifier_2_ac_current
            x: 150
            y: 80
            text: "--.- A"
            text_font: montserrat_18
            text_color: 0x8B96A0

        - label:
            x: 10
            y: 122
            styles: style_desc_label
            text: "DC"

        - label:
            id: ui_rectifier_2_dc_voltage
            x: 65
            y: 120
            text: "--.- V"
            text_font: montserrat_18
            text_color: 0x8B96A0

        - label:
            id: ui_rectifier_2_dc_current
            x: 150
            y: 120
            text: "--.- A"
            text_font: montserrat_18
            text_color: 0x8B96A0

        - label:
            id: ui_rectifier_2_dc_power
            x: 65
            y: 151
            text: "--.-- kW"
            text_font: montserrat_20
            text_color: 0x8B96A0

        - label:
            x: 10
            y: 194
            styles: style_desc_label
            text: "OUT"

        - label:
            id: ui_rectifier_2_temperature
            x: 65
            y: 192
            text: "--.- °C"
            text_font: montserrat_18
            text_color: 0x8B96A0

        - button:
            id: ui_rectifier_2_power_button
            x: 10
            y: 270
            width: 143
            styles: style_dialog_button

            widgets:
              - label:
                  id: ui_rectifier_2_power_button_label
                  align: CENTER
                  text: "UNAVAILABLE"
                  text_font: montserrat_16

            on_short_click:
              - if:
                  condition:
                    lambda: |-
                        return
                          id(ui_model_data_available).state &&
                          id(ui_model_rectifier_2_online).state &&
                          id(ui_model_rectifier_2_power_state).state == "ON";

                  then:
                    - lvgl.widget.show: ui_stop_rectifier_2_dialog

                  else:
                    - lvgl.widget.show: ui_start_rectifier_2_dialog

        - button:
            x: 163
            y: 270
            width: 80
            styles: style_dialog_button

            widgets:
              - label:
                  align: CENTER
                  text: "DETAIL"
                  text_font: montserrat_16

            on_short_click:
              - lambda: |-
                  id(rectifier_detail_unit) = 2;
                  id(ui_active_page) = 2;

              - lvgl.page.show: page_rectifier_detail

              - script.execute:
                  id: refresh_rectifier_detail

  # ---------------------------------------------------------------------------
  # RECTIFIER 3
  # ---------------------------------------------------------------------------

  - obj:
      x: 536
      y: 70
      width: 253
      height: 330
      styles: style_card

      widgets:
        - label:
            x: 10
            y: 10
            styles: style_title_label
            text: "RECTIFIER 3"

        - label:
            id: ui_rectifier_3_lifecycle
            x: 10
            y: 43
            text: "OFFLINE"
            text_font: montserrat_16
            text_color: 0x8B96A0

        - label:
            id: ui_rectifier_3_power_state
            x: 165
            y: 43
            width: 65
            text_align: RIGHT
            text: "--"
            text_font: montserrat_16
            text_color: 0x8B96A0

        - label:
            x: 10
            y: 82
            styles: style_desc_label
            text: "AC"

        - label:
            id: ui_rectifier_3_ac_voltage
            x: 70
            y: 80
            text: "--- V"
            text_font: montserrat_18
            text_color: 0x8B96A0

        - label:
            id: ui_rectifier_3_ac_current
            x: 150
            y: 80
            text: "--.- A"
            text_font: montserrat_18
            text_color: 0x8B96A0

        - label:
            x: 10
            y: 122
            styles: style_desc_label
            text: "DC"

        - label:
            id: ui_rectifier_3_dc_voltage
            x: 70
            y: 120
            text: "--.- V"
            text_font: montserrat_18
            text_color: 0x8B96A0

        - label:
            id: ui_rectifier_3_dc_current
            x: 150
            y: 120
            text: "--.- A"
            text_font: montserrat_18
            text_color: 0x8B96A0

        - label:
            id: ui_rectifier_3_dc_power
            x: 70
            y: 151
            text: "--.-- kW"
            text_font: montserrat_20
            text_color: 0x8B96A0

        - label:
            x: 10
            y: 194
            styles: style_desc_label
            text: "OUT"

        - label:
            id: ui_rectifier_3_temperature
            x: 70
            y: 192
            text: "--.- °C"
            text_font: montserrat_18
            text_color: 0x8B96A0

        - button:
            id: ui_rectifier_3_power_button
            x: 10
            y: 270
            width: 143
            styles: style_dialog_button

            widgets:
              - label:
                  id: ui_rectifier_3_power_button_label
                  align: CENTER
                  text: "UNAVAILABLE"
                  text_font: montserrat_16

            on_short_click:
              - if:
                  condition:
                    lambda: |-
                        return
                          id(ui_model_data_available).state &&
                          id(ui_model_rectifier_3_online).state &&
                          id(ui_model_rectifier_3_power_state).state == "ON";

                  then:
                    - lvgl.widget.show: ui_stop_rectifier_3_dialog

                  else:
                    - lvgl.widget.show: ui_start_rectifier_3_dialog

        - button:
            x: 163
            y: 270
            width: 80
            styles: style_dialog_button

            widgets:
              - label:
                  align: CENTER
                  text: "DETAIL"
                  text_font: montserrat_16

            on_short_click:
              - lambda: |-
                  id(rectifier_detail_unit) = 3;
                  id(ui_active_page) = 2;

              - lvgl.page.show: page_rectifier_detail

              - script.execute:
                  id: refresh_rectifier_detail
