anwa/esphome-r4875g1-3phase-charger/packages/display/theme.yaml

# ==============================================================================
# SHARED LVGL THEME
# ==============================================================================
#
# Shared visual styles used by the Charger Controller and Remote HMI.
# ==============================================================================

lvgl:
  theme:
    button:
      pressed:
        bg_color: 0x3A4652

      disabled:
        # Keep disabled buttons visually muted without the additional LVGL
        # default-theme filter brightening the configured colors.
        bg_color: 0x161B20
        bg_opa: COVER
        border_color: 0x2C353D
        border_opa: COVER
        text_color: 0x68727B
        color_filter_opa: TRANSP
        recolor_opa: TRANSP

    spinbox:
      cursor:
        bg_color: 0x3A4652
        bg_opa: COVER
        text_color: 0xFFFFFF

  style_definitions:

    # ---------------------------------------------------------------------------
    # MAIN PAGE BACKGROUND
    # ---------------------------------------------------------------------------

    - id: style_page
      bg_color: 0x101418
      bg_opa: COVER
      border_width: 0
      pad_all: 0

    # ---------------------------------------------------------------------------
    # PERSISTENT TOP HEADER
    # ---------------------------------------------------------------------------

    - id: style_header
      bg_color: 0x171D23
      bg_opa: COVER
      border_width: 0
      radius: 0
      pad_all: 0

    # ---------------------------------------------------------------------------
    # BOTTOM NAVIGATION BUTTONS
    # ---------------------------------------------------------------------------

    - id: style_nav_button
      width: 120
      height: 58
      bg_color: 0x202830
      bg_opa: COVER
      border_color: 0x3B4652
      border_width: 1
      radius: 8
      text_color: 0xDDE3E8
      text_font: montserrat_18

    # ---------------------------------------------------------------------------
    # GENERIC CONTENT CARD
    # ---------------------------------------------------------------------------

    - id: style_card
      bg_color: 0x171D23
      bg_opa: COVER
      border_color: 0x303A44
      border_width: 1
      radius: 12
      pad_all: 0

    # ---------------------------------------------------------------------------
    # DIALOG PANEL
    # ---------------------------------------------------------------------------

    - id: style_dialog_panel
      bg_color: 0x202830
      bg_opa: COVER
      border_color: 0x4A5662
      border_width: 2
      radius: 10
      pad_all: 0

    # ---------------------------------------------------------------------------
    # SHARED ACTION BUTTON
    # ---------------------------------------------------------------------------

    - id: style_dialog_button
      width: 140
      height: 50
      bg_color: 0x202830
      bg_opa: COVER
      border_color: 0x4A5662
      border_width: 1
      radius: 8
      text_color: 0xFFFFFF
      text_font: montserrat_16

    # ---------------------------------------------------------------------------
    # SHARED STEP BUTTON
    # ---------------------------------------------------------------------------

    - id: style_dialog_step_button
      width: 50
      height: 50
      bg_color: 0x202830
      bg_opa: COVER
      border_color: 0x4A5662
      border_width: 1
      radius: 8
      text_color: 0xFFFFFF
      text_font: montserrat_20

    # ---------------------------------------------------------------------------
    # DIALOG SPINBOX
    # ---------------------------------------------------------------------------

    - id: style_dialog_spinbox
      bg_color: 0x171D23
      bg_opa: COVER
      border_color: 0x4A5662
      border_width: 1
      radius: 8
      text_color: 0xFFFFFF
      text_font: montserrat_18

    # ---------------------------------------------------------------------------
    # TITLE LABEL
    # ---------------------------------------------------------------------------

    - id: style_title_label
      text_color: 0x8B96A0
      text_font: montserrat_18

    # ---------------------------------------------------------------------------
    # DESC LABEL
    # ---------------------------------------------------------------------------

    - id: style_desc_label
      text_color: 0x8B96A0
      text_font: montserrat_14

    # ---------------------------------------------------------------------------
    # VALUE LABEL
    # ---------------------------------------------------------------------------

    - id: style_value_label
      text_color: 0xFFFFFF
      text_font: montserrat_18
      text_align: RIGHT
